AllenNeuralDynamics/harp.device.white-rabbit/firmware/src/white_rabbit_app.cpp

#include "white_rabbit_app.h"

// Apply starting values.
uint32_t counter_interval_us = 0;
uint64_t last_msg_emit_time_us;
bool was_synced = false;

app_regs_t app_regs;

// Define "specs" per-register
RegSpec app_reg_specs[]
{
    RegSpec::U16(&app_regs.ConnectedDevices,
        HarpCore::read_reg_generic, HarpCore::write_reg_generic), // 32
    RegSpec::U32(&app_regs.Counter,
        HarpCore::read_reg_generic, HarpCore::write_reg_generic), // 33
    RegSpec::U16(&app_regs.CounterFrequencyHz,
       HarpCore::read_reg_generic, write_counter_frequency_hz),
    RegSpec::U8(&app_regs.AuxPortFn,
        HarpCore::read_reg_generic, write_aux_port_fn),
    RegSpec::U32(&app_regs.AuxBaudRate,
        HarpCore::read_reg_generic, write_aux_baud_rate),
    // More specs here if we add additional registers.
};

const size_t APP_REG_COUNT = std::size(app_reg_specs);

// Harp CLKout Double Buffer Setup
volatile int __not_in_flash("double_buffers") harp_clkout_dma_chan = -1;

int32_t __not_in_flash("double_buffers") harp_clkout_alarm_num = -1;
uint32_t __not_in_flash("double_buffers") harp_clkout_irq_number;

volatile uint8_t __not_in_flash("double_buffers") harp_time_msg_a[6] =
    {0xAA, 0xAF, 0x00, 0x00, 0x00, 0x00};
volatile uint8_t __not_in_flash("double_buffers") harp_time_msg_b[6] =
    {0xAA, 0xAF, 0x00, 0x00, 0x00, 0x00};

volatile uint8_t __not_in_flash("double_buffers") *dispatch_buffer;
volatile uint8_t __not_in_flash("double_buffers") *load_buffer;

// AUX CLKout Double Buffer Setup
volatile int __not_in_flash("double_buffers") aux_clkout_dma_chan = -1;

int32_t __not_in_flash("double_buffers") aux_clkout_alarm_num = -1;
uint32_t __not_in_flash("double_buffers") aux_clkout_irq_number;

volatile uint32_t __not_in_flash("double_buffers") aux_clkout_seconds_a;
volatile uint32_t __not_in_flash("double_buffers") aux_clkout_seconds_b;

volatile uint32_t __not_in_flash("double_buffers") *dispatch_second;
volatile uint32_t __not_in_flash("double_buffers") *load_second;

// AUX CLKout software implementation.
SoftUART soft_uart = SoftUART(AUX_PIN);

// PPS Alarm/IRQ resources
int32_t __not_in_flash("double_buffers") pps_output_alarm_num = -1;
uint32_t __not_in_flash("double_buffers") pps_output_irq_number;


void setup_harp_clkout()
{
    // Setup DMA.
    if (harp_clkout_dma_chan < 0) // Claim a DMA channel if not yet claimed.
        harp_clkout_dma_chan = dma_claim_unused_channel(true);
    // Setup UART TX for periodic transmission of the time at 100KBaud.
    uart_inst_t* uart_id = HARP_UART;
    // Do **not** reinitialize the UART since this uart is shared with the
    // synchronizer.
    if (!uart_is_enabled(uart_id))
        uart_init(uart_id, HARP_SYNC_BAUDRATE);
    uart_set_hw_flow(uart_id, false, false);
    uart_set_fifo_enabled(uart_id, false); // Set FIFO size to 1.
    uart_set_format(uart_id, 8, 1, UART_PARITY_NONE);
    gpio_set_function(HARP_CLKOUT_PIN, GPIO_FUNC_UART);
    // Setup Outgoing msg double buffer;
    dispatch_buffer = &(harp_time_msg_a[0]);
    load_buffer = &(harp_time_msg_b[0]);
    // Setup Harp CLKOUT periodic outgoing time message.
    // Leverage RP2040 ALARMs to dispatch periodically via interrupt handler.
    // Tell Pico-SDK that we are using this alarm.
    if (harp_clkout_alarm_num < 0)
        harp_clkout_alarm_num = hardware_alarm_claim_unused(true);
    // TODO: harp_clkout_irq_number = TIMER_IRQ_NUM(timer_hw, harp_clkout_alarm_num);
    harp_clkout_irq_number = TIMER_IRQ_0 + harp_clkout_alarm_num;
#if defined(DEBUG)
    printf("harp clkout alarm num: %d | irq num: %d\r\n", harp_clkout_alarm_num,
           harp_clkout_irq_number);
#endif
    // Attach interrupt to function and enable alarm to generate interrupt.
    irq_set_exclusive_handler(harp_clkout_irq_number,
                              dispatch_and_reschedule_harp_clkout);
    irq_set_enabled(harp_clkout_irq_number, true);
    // Compute start time for Harp CLKOUT msg.
    // Get the next whole second.
    uint32_t curr_harp_seconds = HarpCore::harp_time_s();
    uint64_t next_msg_harp_time_us = (uint64_t(curr_harp_seconds) * 1'000'000UL)
                                     + 1'000'000UL;
    // Offset such that the start of last byte occurs on the whole second per:
    // https://harp-tech.org/protocol/SynchronizationClock.html#serial-configuration
    next_msg_harp_time_us += HARP_SYNC_START_OFFSET_US;
    // Compute the time sent in the actual msg.
    // Note that we are dispatching the **next** second that takes place
    // after the msg has been sent.
    uint32_t harp_timestamp_msg = curr_harp_seconds + 1;
    // Load the first msg to dispatch. Subsequent loads will go into the
    //  load_buffer.
    memcpy((void*)(dispatch_buffer + 2), (void*)(&harp_timestamp_msg),
           sizeof(curr_harp_seconds));
    // Schedule next time msg dispatch in system time.
    // Low-level interface (fast!) to re-schedule this function.
    uint32_t alarm_time_us = HarpCore::harp_to_system_us_32(next_msg_harp_time_us);
    // Enable alarm to trigger interrupt.
    timer_hw->inte |= (1u << harp_clkout_alarm_num);
    // Arm alarm by writing the alarm time.
    timer_hw->alarm[harp_clkout_alarm_num] = alarm_time_us;
}

void __not_in_flash_func(dispatch_and_reschedule_harp_clkout)()
{
    // Dispatch the previously-configured time.
    dispatch_uart_stream(harp_clkout_dma_chan, HARP_UART,
                         (uint8_t*)dispatch_buffer, 6);
    // Clear the latched hardware interrupt.
    timer_hw->intr = (1u << harp_clkout_alarm_num);
    // Get the next whole harp time second. +2 because we wake up *before* the
    // elapse of the next whole second when we are supposed to emit the msg.
    uint32_t curr_harp_seconds = HarpCore::harp_time_s();
    uint64_t next_msg_harp_time_us = (uint64_t(curr_harp_seconds) * 1'000'000UL)
                                     + 2'000'000UL;
#if defined(DEBUG)
    printf("Sending: %x %x %x %x %x %x\r\n", dispatch_buffer[0],
           dispatch_buffer[1], dispatch_buffer[2], dispatch_buffer[3],
           dispatch_buffer[4], dispatch_buffer[5]);
#endif
    // Offset such that the start of last byte occurs on the whole second per:
    // https://harp-tech.org/protocol/SynchronizationClock.html#serial-configuration
    next_msg_harp_time_us += HARP_SYNC_START_OFFSET_US;
    // Compute the time sent in the actual msg.
    // Note that we are dispatching the **next** second that takes place
    // after the msg has been sent.
    uint32_t harp_timestamp_msg = curr_harp_seconds + 1;
    // Update time contents in the next message.
    memcpy((void*)(load_buffer + 2), (void*)(&harp_timestamp_msg),
           sizeof(curr_harp_seconds));
    // Toggle ping-pong buffers.
    std::swap(load_buffer, dispatch_buffer);
    // Schedule next time msg dispatch in system time.
    // Low-level interface (fast!) to re-schedule this function.
    uint32_t alarm_time_us = HarpCore::harp_to_system_us_32(next_msg_harp_time_us);
    // Enable alarm to trigger interrupt.
    timer_hw->inte |= (1u << harp_clkout_alarm_num);
    // Arm alarm by writing the alarm time.
    timer_hw->alarm[harp_clkout_alarm_num] = alarm_time_us;
}

void setup_aux_clkout()
{
    // Setup DMA.
    if (aux_clkout_dma_chan < 0) // Claim a DMA channel if not yet claimed.
        aux_clkout_dma_chan = dma_claim_unused_channel(true);
    // Update baud rate (if it has changed).
    soft_uart.reset();
    soft_uart.set_baud_rate(app_regs.AuxBaudRate);
    // Setup AUX CLKOUT periodic outgoing time message.
    // Setup Outgoing msg double buffer;
    dispatch_second = &aux_clkout_seconds_a;
    load_second = &aux_clkout_seconds_b;
    // Setup AUX CLKOUT periodic outgoing time message.
    // Leverage RP2040 ALARMs to dispatch periodically via interrupt handler.
    // Tell Pico-SDK that we are using this alarm.
    if (aux_clkout_alarm_num < 0)
        aux_clkout_alarm_num = hardware_alarm_claim_unused(true);
    // TODO: aux_clkout_irq_number = TIMER_IRQ_NUM(timer_hw, aux_clkout_alarm_num);
    aux_clkout_irq_number = TIMER_IRQ_0 + aux_clkout_alarm_num;
    // Attach interrupt to function and enable alarm to generate interrupt.
    irq_set_exclusive_handler(aux_clkout_irq_number,
                              dispatch_and_reschedule_aux_clkout);
    irq_set_enabled(aux_clkout_irq_number, true);
    // Compute start time for AUX CLKOUT msg.
    // Get the next whole second.
    uint32_t curr_harp_seconds = HarpCore::harp_time_s(); // Note: rounds down.
    // Load initial value to be dispatched at the start of the next second.
    *dispatch_second = curr_harp_seconds + 1;
    uint64_t next_msg_harp_time_us = (uint64_t(curr_harp_seconds) * 1'000'000UL)
                                     + 1'000'000UL;
    // Apply additional offset if any.
    next_msg_harp_time_us += AUX_SYNC_START_OFFSET_US;
    // Schedule next time msg dispatch in system time.
    // Low-level interface (fast!) to re-schedule this function.
    uint32_t alarm_time_us = HarpCore::harp_to_system_us_32(next_msg_harp_time_us);
    // Enable alarm to trigger interrupt.
    timer_hw->inte |= (1u << aux_clkout_alarm_num);
    // Arm alarm by writing the alarm time.
    timer_hw->alarm[aux_clkout_alarm_num] = alarm_time_us;
}

void __not_in_flash_func(dispatch_and_reschedule_aux_clkout)()
{
    // Dispatch the previously-configured time.
    soft_uart.send((uint8_t*)dispatch_second, sizeof(dispatch_second));

    // Clear the latched hardware interrupt.
    timer_hw->intr = (1u << aux_clkout_alarm_num);
    // Compute the *next* whole harp time second.
    uint32_t curr_harp_seconds = HarpCore::harp_time_s(); // Note: rounds down.
    uint64_t next_msg_harp_time_us = (uint64_t(curr_harp_seconds) * 1'000'000UL)
                                     + 1'000'000UL;
    // Account for extra second if we wake up *before* the elapse of the next
    // whole second.
    if (AUX_SYNC_START_OFFSET_US < 0)
        next_msg_harp_time_us += 1'000'000UL;
    // Add offset (if any).
    next_msg_harp_time_us += AUX_SYNC_START_OFFSET_US;
    // Update time contents in the next message.
    // Note that this value will fire on the next occurence of this ISR, so we
    // need to load the *next* second.
    *load_second = curr_harp_seconds + 1;
    // Toggle ping-pong buffers.
    std::swap(load_second, dispatch_second);
    // Schedule next time msg dispatch in system time.
    // Low-level interface (fast!) to re-schedule this function.
    uint32_t alarm_time_us = HarpCore::harp_to_system_us_32(next_msg_harp_time_us);
    // Enable alarm to trigger interrupt.
    timer_hw->inte |= (1u << aux_clkout_alarm_num);
    // Arm alarm by writing the alarm time.
    timer_hw->alarm[aux_clkout_alarm_num] = alarm_time_us;

}

void cleanup_aux_clkout()
{
    // Bail early if resources have not been allocated for this behavior.
    if (aux_clkout_alarm_num < 0)
        return;
    // Disarm alarm by writing 1 to the corresponding alarm.
    timer_hw->armed = (1u << aux_clkout_alarm_num);
    // Clear the latched hardware interrupt (if latched).
    timer_hw->intr = (1u << aux_clkout_alarm_num);
    // Disable alarm to trigger interrupt.
    timer_hw->inte &= ~(1u << aux_clkout_alarm_num);
    // Unreserve Alarm and IRQ if it was not yet claimed.
    hardware_alarm_unclaim(aux_clkout_alarm_num);
    aux_clkout_alarm_num = -1;
    irq_set_enabled(aux_clkout_irq_number, false);
    irq_remove_handler(aux_clkout_irq_number,
                       dispatch_and_reschedule_aux_clkout);
    soft_uart.cleanup();
    gpio_deinit(AUX_PIN);
}

void setup_pps_output()
{
    // Setup GPIO pins.
    gpio_init(LED0_PIN);
    gpio_set_dir(LED0_PIN, GPIO_OUT);
    gpio_put(LED0_PIN, 0);
#if !defined(DEBUG)
    gpio_init(AUX_PIN); // shared with PPS.
    gpio_set_dir(AUX_PIN, GPIO_OUT);
    gpio_put(AUX_PIN, 0);
#endif
    // Setup Harp CLKOUT periodic outgoing time message.
    // Leverage RP2040 ALARMs to dispatch periodically via interrupt handler.
    // Tell Pico-SDK that we are using this alarm.
    if (pps_output_alarm_num < 0)
        pps_output_alarm_num = hardware_alarm_claim_unused(true);
    // TODO: pps_output_irq_number = TIMER_IRQ_NUM(timer_hw, harp_clkout_alarm_num);
    pps_output_irq_number = TIMER_IRQ_0 + pps_output_alarm_num;
#if defined(DEBUG)
    printf("PPS output alarm num: %d | irq num: %d\r\n", pps_output_alarm_num,
           pps_output_irq_number);
#endif
    // Attach interrupt to function and enable alarm to generate interrupt.
    irq_set_exclusive_handler(pps_output_irq_number, update_pps_output);
    irq_set_enabled(pps_output_irq_number, true);
    // Compute start time for PPS Output (next whole second).
    // Get the next whole second.
    uint32_t curr_harp_seconds = HarpCore::harp_time_s();
    uint64_t next_msg_harp_time_us = (uint64_t(curr_harp_seconds) * 1'000'000UL)
                                     + 1'000'000UL;
    // Schedule next time msg dispatch in system time.
    // Low-level interface (fast!) to re-schedule this function.
    uint32_t alarm_time_us = HarpCore::harp_to_system_us_32(next_msg_harp_time_us);
    // Enable alarm to trigger interrupt.
    timer_hw->inte |= (1u << pps_output_alarm_num);
    // Arm alarm by writing the alarm time.
    timer_hw->alarm[pps_output_alarm_num] = alarm_time_us;
}

void __not_in_flash_func(update_pps_output)()
{
    // Toggle GPIO Pins.
#if defined(DEBUG)
    // Only toggle LED pin if DEBUG port is used for debug UART.
    gpio_xor_mask(1u << LED0_PIN);
#else
    gpio_xor_mask((1u << AUX_PIN) | (1u << LED0_PIN));
#endif
    // Clear the latched hardware interrupt.
    timer_hw->intr = (1u << pps_output_alarm_num);
    // Schedule next update.
    // Get the next whole harp time **half**-second.
    // Round down. i.e: integer-divide into half-second multiples and add 0.5s.
    uint64_t next_msg_harp_time_us =
#if defined(PICO_RP2040)
        div_u64u64(HarpCore::harp_time_us_64(), 500'000UL) * 500'000UL + 500'000UL;
#else
        (HarpCore::harp_time_us_64() / 500'000UL) * 500'000UL + 500'000UL;
#endif
    // Schedule next time msg dispatch in system time.
    // Low-level interface (fast!) to re-schedule this function.
    uint32_t alarm_time_us = HarpCore::harp_to_system_us_32(next_msg_harp_time_us);
    // Enable alarm to trigger interrupt.
    timer_hw->inte |= (1u << pps_output_alarm_num);
    // Arm alarm by writing the alarm time.
    timer_hw->alarm[pps_output_alarm_num] = alarm_time_us;
}

void cleanup_pps_output()
{
    // Bail early if resources have not been allocated for this behavior.
    if (pps_output_alarm_num < 0)
        return;
    // Disarm alarm by writing 1 to the corresponding alarm.
    timer_hw->armed = (1u << pps_output_alarm_num);
    // Clear the latched hardware interrupt (if latched).
    timer_hw->intr = (1u << pps_output_alarm_num);
    // Disable alarm to trigger interrupt.
    timer_hw->inte &= ~(1u << pps_output_alarm_num);
    // Unreserve Alarm and IRQ.
    hardware_alarm_unclaim(pps_output_alarm_num);
    pps_output_alarm_num = -1;
    irq_set_enabled(pps_output_irq_number, false);
    irq_remove_handler(pps_output_irq_number, update_pps_output);
#if !defined(DEBUG)
    gpio_deinit(AUX_PIN); // shared with PPS.
#endif
    gpio_deinit(LED0_PIN); // shared with PPS.
}

void write_counter_frequency_hz(msg_t& msg)
{
    HarpCore::copy_msg_payload_to_register(msg);
    // Cap maximum value.
    if (app_regs.CounterFrequencyHz > MAX_EVENT_FREQUENCY_HZ)
    {
        app_regs.CounterFrequencyHz = MAX_EVENT_FREQUENCY_HZ;
        // Update pre-computed interval.
        counter_interval_us =
#if defined(PICO_RP2040)
            div_u64u64(1'000'000ULL, app_regs.CounterFrequencyHz);
#else
            1'000'000ULL / app_regs.CounterFrequencyHz;
#endif
        last_msg_emit_time_us = HarpCore::harp_time_us_64(); // reset interval.
        HarpCore::send_harp_reply(WRITE_ERROR, msg.header.address);
        return;
    }
    // Update pre-computed interval.
    counter_interval_us =
#if defined(PICO_RP2040)
    div_u64u64(1'000'000ULL, app_regs.CounterFrequencyHz);
#else
    1'000'000ULL / app_regs.CounterFrequencyHz;
#endif
    last_msg_emit_time_us = HarpCore::harp_time_us_64();
    if (!HarpCore::is_muted())
        HarpCore::send_harp_reply(WRITE, msg.header.address);
}

void write_aux_port_fn(msg_t& msg)
{
    uint8_t old_aux_fn = app_regs.AuxPortFn;
    HarpCore::copy_msg_payload_to_register(msg);
    // Only 0, 1, and 2 are valid options.
    if (app_regs.AuxPortFn > 2)
    {
        if (!HarpCore::is_muted())
            HarpCore::send_harp_reply(WRITE_ERROR, msg.header.address);
        app_regs.AuxPortFn = old_aux_fn; // Restore original setting.
        return; // Bail early.
    }
    // Nothing new to do!
    if (app_regs.AuxPortFn == old_aux_fn)
    {
        if (!HarpCore::is_muted())
            HarpCore::send_harp_reply(WRITE, msg.header.address);
        return;
    }
    reset_aux_fn(); // Always do this before reconfiguring.
    switch (app_regs.AuxPortFn)
    {
        case 0: // Clear behaviors.
            // already handled by reset_aux_fn() above.
            break;
        case 1: // AUX CLKout.
#if !defined(DEBUG) // DEBUG mode claims this UART.
            setup_aux_clkout();
#endif
            break;
        case 2: // PPS Ouput.
            setup_pps_output();
            break;
    }
    if (!HarpCore::is_muted())
        HarpCore::send_harp_reply(WRITE, msg.header.address);
}

void write_aux_baud_rate(msg_t& msg)
{
    uint32_t old_baud_rate = app_regs.AuxBaudRate;
    HarpCore::copy_msg_payload_to_register(msg);
    // Reject invalid baud rates.
    if (app_regs.AuxBaudRate < MIN_AUX_SYNC_BAUDRATE ||
        app_regs.AuxBaudRate > MAX_AUX_SYNC_BAUDRATE)
    {
        if (!HarpCore::is_muted())
            HarpCore::send_harp_reply(WRITE_ERROR, msg.header.address);
        app_regs.AuxBaudRate = old_baud_rate; // Keep the old baud rate.
        return;
    }
#if !defined(DEBUG)
    cleanup_aux_clkout(); // Disable AUX CLKout.
    setup_aux_clkout(); // Reinitialize AUX CLKout on new baud rate.
#endif
    if (!HarpCore::is_muted())
        HarpCore::send_harp_reply(WRITE, msg.header.address);
}

void update_app_state()
{
    if (soft_uart.requires_update())
        soft_uart.update();
    // Update the state of ConnectedDevices.
    uint16_t old_port_raw = app_regs.ConnectedDevices;
    uint32_t port_raw = gpio_get_all();
    // CHAN[7:0] = GPIO[23:16]; CHAN[8:15] = GPIO[15:8]. See schematic.
    port_raw >>= 8;
    port_raw = ((port_raw & 0x000000FF) << 8) | ((port_raw & 0x0000FF00) >> 8);
    app_regs.ConnectedDevices = uint16_t(port_raw);
    // If port state changed, dispatch event from ConnectedDevices app reg (32).
    // TODO: add hysteresis.
    if ((old_port_raw != app_regs.ConnectedDevices) && !HarpCore::is_muted())
        HarpCore::send_harp_reply(EVENT, HarpCore::APP_REG_START_ADDRESS);

    // Nothing to do if we're not instructed to emit periodic msgs.
    if (app_regs.CounterFrequencyHz == 0)
        return;
    uint64_t curr_time_us = HarpCore::harp_time_us_64();
    // Handle edge-case where we went from not-synced to synced.
    if (HarpSynchronizer::is_synced() && !was_synced)
    {
        was_synced = true;
        // Get a new time value to avoid race condition with old curr_time_us.
        curr_time_us = HarpCore::harp_time_us_64();
        last_msg_emit_time_us = curr_time_us; // reset counter.
    }
    // Handle periodic counter msg dispatch.
    if (int64_t(curr_time_us - last_msg_emit_time_us) >= counter_interval_us)
    {
        last_msg_emit_time_us += counter_interval_us;
        app_regs.Counter += 1;
        // Issue EVENT from Counter register.
        if (!HarpCore::is_muted())
            HarpCore::send_harp_reply(EVENT, HarpCore::APP_REG_START_ADDRESS + 1);
    }
}

void reset_aux_fn()
{
    cleanup_pps_output();
#if !defined(DEBUG)
    cleanup_aux_clkout(); // Cleanup lingering AUX CLKout behavior.
#endif
}

void reset_app()
{
    counter_interval_us = 0;
    app_regs.Counter = 0;
    app_regs.CounterFrequencyHz = 0;
    setup_harp_clkout();
#if defined(DEBUG)
    app_regs.AuxPortFn = 0; // Start with AUX CLKout disabled.
#else
    app_regs.AuxPortFn = 1; // Start with AUX CLKout fn enabled.
#endif
    app_regs.AuxBaudRate = AUX_SYNC_DEFAULT_BAUDRATE;
    reset_aux_fn();
#if !defined(DEBUG)
    setup_aux_clkout(); // Start with AUX CLKout fn enabled.
#endif
}
